simoninns/vp415-emulator/fpga/vp415-fpga/src/aivvideo.v

/************************************************************************
	
	aivvideo.v
	Top module
	
	VP415-Emulator FPGA
	Copyright (C) 2025 Simon Inns
	
	This file is part of VP415-Emulator.
	
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
	Email: simon.inns@gmail.com
	
************************************************************************/

// Disable Verilog implicit definitions
`default_nettype none

module aivvideo (
    input sysClk,
    input nReset,
    input [2:0] sysClkPhase,

    input [2:0] rgb_111,
    input csync,

    input displayEnable_pi, // Active high when in the active display area
    input frame_start_flag_pi, // Start of frame flag

    // SRAM interface
    output [17:0] SRAM0_A,
    inout [15:0] SRAM0_D,
    output SRAM0_nCS,
    output SRAM0_nOE,
    output SRAM0_nWE,

    output [17:0] rgb_666, // 18-bit RGB666 output
    output frame_start_flag_aiv,
);

    // -----------------------------------------------------------
    // Syncronize the incoming AIV async signals to the Pi's pixel clock
    // This is done using a 2-stage synchronizer to avoid metastability
    // issues.
    wire [2:0] rgb_sync_111;
    wire aiv_csyncIn_sync;

    sync_signals sync_signals0 (
        // Inputs (asynchronous)
        .clk(sysClk),
        .rgb_111(rgb_111),
        .csync(csync),

        // Outputs (synchronous to clk)
        .rgb_sync_111(rgb_sync_111),
        .csync_sync(aiv_csyncIn_sync)
    );

    // -----------------------------------------------------------
    // PAL 576i hsync/vsync regeneration from incoming AIV composite sync
    wire hsync_aiv;
    wire vsync_aiv;
    wire isFieldOdd_aiv;

    sync_regenerator_pal576i sync_regenerator_pal576i0 (
        // Inputs
        .clk(sysClk),
        .clkPhase(sysClkPhase),
        .csync(aiv_csyncIn_sync),

        // Outputs
        .hsync(hsync_aiv),
        .vsync(vsync_aiv),
        .isFieldOdd(isFieldOdd_aiv)
    );

    // -----------------------------------------------------------
    // Generate AIV pixel x,y and display enable signals
    wire [9:0] pixelX_aiv;
    wire [9:0] pixelY_aiv;
    wire displayEnable_aiv; // Active high when in the active display area
    wire frame_start_flag_aiv; // Start of frame flag

    aiv_active_frame_tracker aiv_active_frame_tracker0 (
        // Inputs
        .clk(sysClk),
        .clkPhase(sysClkPhase),
        .nReset(nReset),
        .hsync(hsync_aiv),
        .vsync(vsync_aiv),
        .isFieldOdd(isFieldOdd_aiv),

        // Outputs
        .active_frame_dot(pixelX_aiv),
        .active_frame_line(pixelY_aiv),
        .display_enable(displayEnable_aiv),
        .frame_start_flag(frame_start_flag_aiv),
    );

    // -----------------------------------------------------------
    // Test card generator
    wire [2:0] rgb_testcard_111;

    testcard1bit testcard1bit0 (
        // Inputs
        .clk(sysClk),
        .nReset(nReset),
        .pixelX(pixelX_aiv),
        .pixelY(pixelY_aiv),
        .displayEnable(displayEnable_aiv),

        // Outputs
        .rgb_111(rgb_testcard_111)
    );

    // -----------------------------------------------------------
    // Frame buffer for the RGB111 signals
    wire [2:0] rgb_fb_111;

    framebuffer framebuffer0 (
        // Inputs
        .clk(sysClk),
        .clkPhase(sysClkPhase),
        .reset_n(nReset),

        .display_en_in(displayEnable_aiv),
        .display_en_out(displayEnable_pi),

        .frame_start_flag_in(frame_start_flag_aiv),
        .frame_start_flag_out(frame_start_flag_pi),

        .rgb_111_in(rgb_sync_111),
        //.rgb_111_in(rgb_testcard_111),
        .rgb_111_out(rgb_fb_111),
        
        // SRAM interface signals
        .sram_addr(SRAM0_A),
        .sram_data(SRAM0_D),
        .sram_ce_n(SRAM0_nCS),
        .sram_oe_n(SRAM0_nOE),
        .sram_we_n(SRAM0_nWE)
    );

    // -----------------------------------------------------------
    // Convert the RGB111 output to RGB666 and output to SCART
    rgb111to666 rgb111to6660 (
        // Inputs
        .clk(sysClk),
        .rgb_111(rgb_fb_111),

        // Outputs
        .rgb_666(rgb_666)
    );

endmodule
